pam-param-pam/Tally-light/esp8266/ATEM_tally_light/ATEM_tally_light.hpp

/*
    Copyright (C) 2023 Aron N. Het Lam, aronhetlam@gmail.com

    This program makes an ESP8266 into a wireless tally light system for ATEM switchers,
    by using Kasper Skårhøj's (<https://skaarhoj.com>) ATEM client libraries for Arduino.

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
    You should have received a copy of the GNU General Public License
    along with this program.  If not, see <https://www.gnu.org/licenses/>.
*/

#include "Arduino.h"
//Perform initial setup on power on
//Handle the change of states in the program
void changeState(uint8_t stateToChangeTo);

//Websocket event, on connect, on disconnect, on text, on binary etc
//void webSocketEvent(WStype_t type, uint8_t * payload, size_t length);

//Loop that checks for button press
void buttonLoop();

//Set the color of both LEDs
void setLedColor(uint8_t color);

//Set the color of a LED using the given pins
void setLED(uint8_t color, int pinRed, int pinGreen, int pinBlue);

void analogWriteWrapper(uint8_t pin, uint8_t value);

int getTallyState(uint16_t tallyNo);

int getLedColor(int tallyNo);

//Serve setup web page to client, by sending HTML with the correct variables
void handleRoot();

//Save new settings from client in EEPROM and restart the ESP8266 module
void handleSave();

//Send 404 to client in case of invalid webpage being requested.
void handleNotFound();

String getSSID();

void setWiFi(String ssid, String pwd);

// void improvCallback(improv::ImprovCommand d);
//Commented out for users without batteries - Also timer is not done properly
//Main loop for things that should work every second
void batteryLoop();
